V3n0m1010011010/E-Paper-Dev-Board/esp32_epaper_board/kicad/e-paper-esp32/e-paper-esp32.pdf

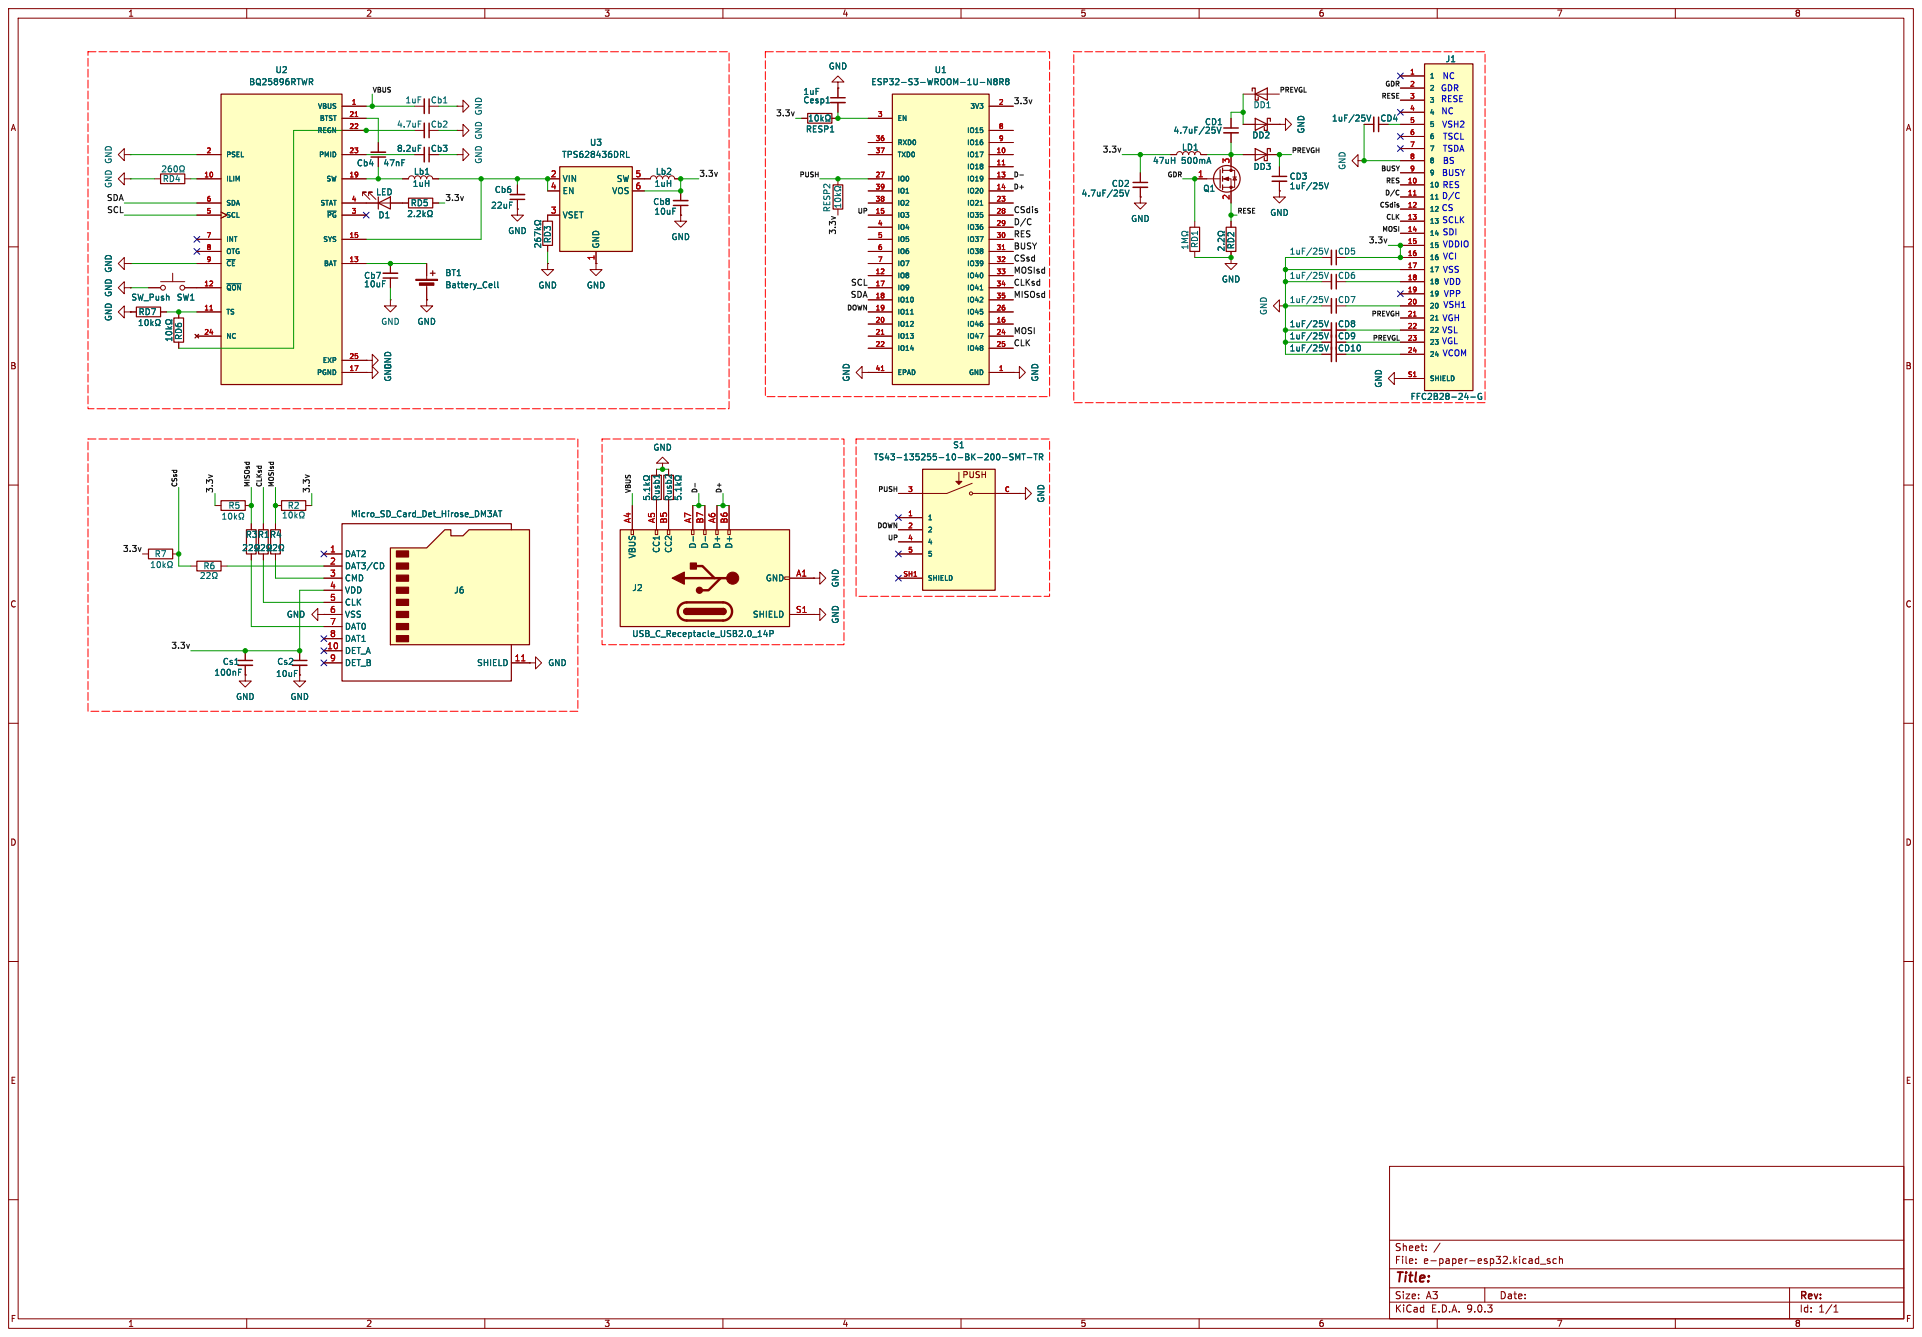
[picture p11: page 1]

1 SW 5 VOS 6 U3 TPS628436DRL RD3 þÿ267k© GND GND GND VBUS

1 SW 5 VOS 6 RD3 þÿ267k© GND

10uFGND GND þÿ5.1k© Rusb1 Rusb2 þÿ5.1k© GND GND

Id: 1/1 Title: File: e-paper-esp32.kicad_sch Sheet: /
