V3n0m1010011010/E-Paper-Dev-Board/esp32_epaper_board/Docs/Plott/e-paper-esp32.pdf

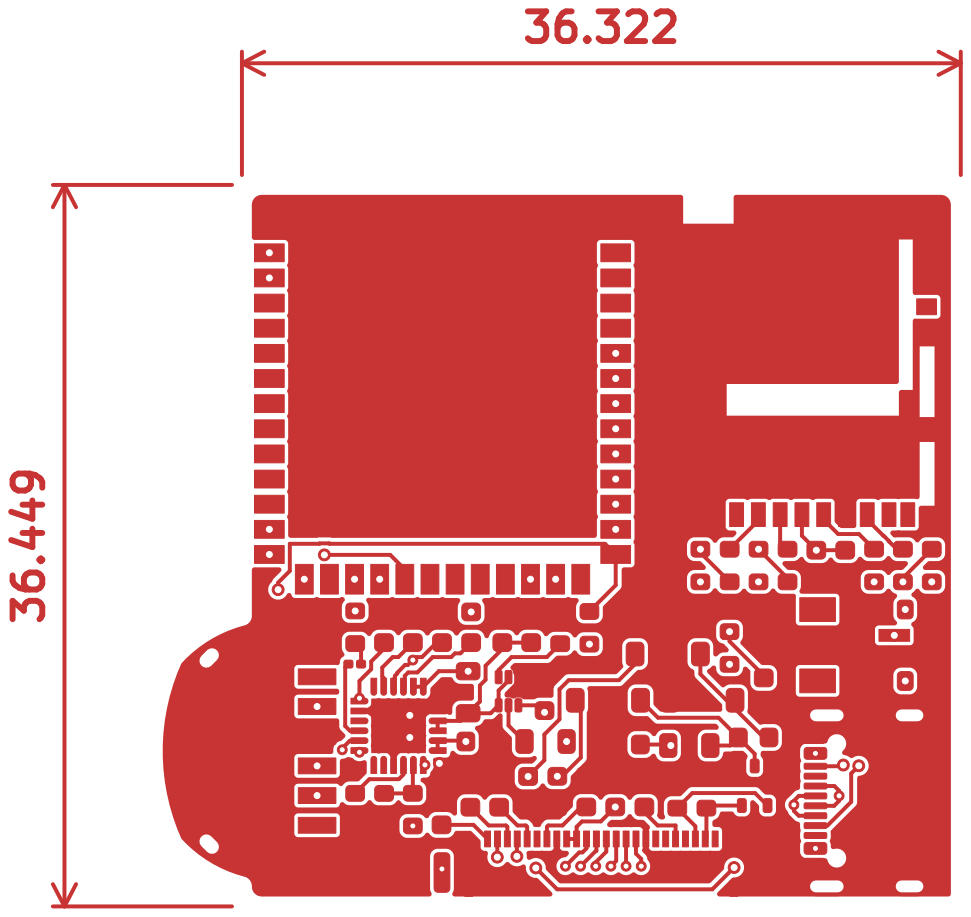
[picture p12: page 1]

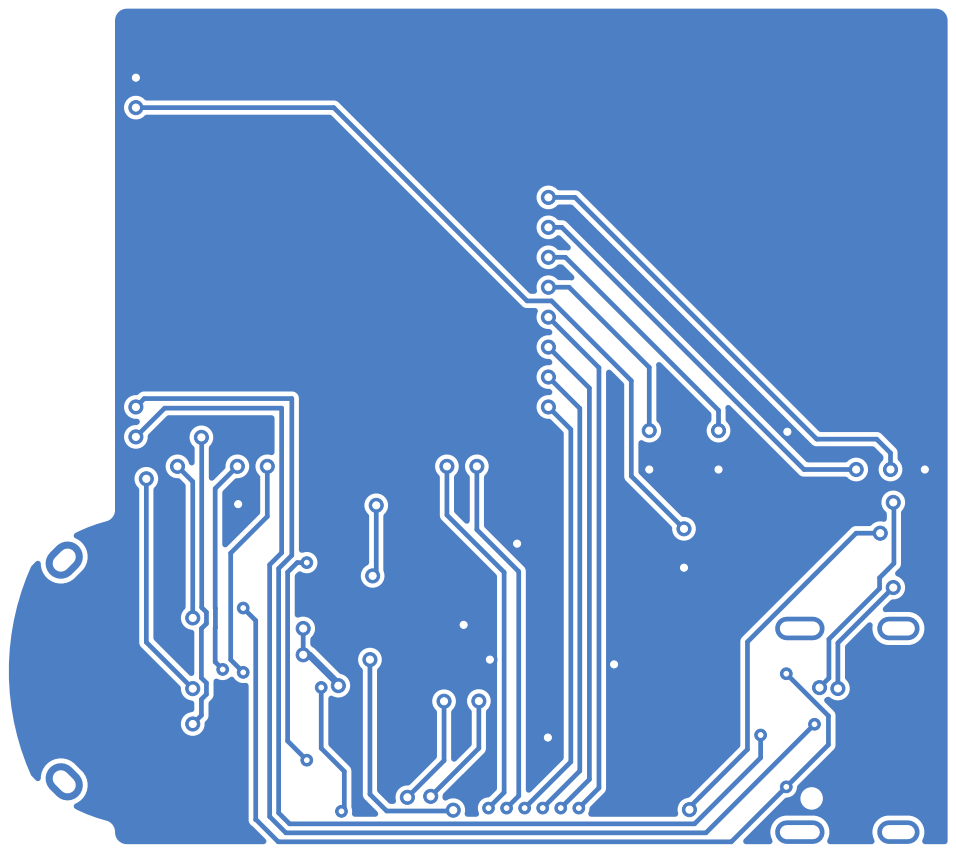
[picture p13: page 2]

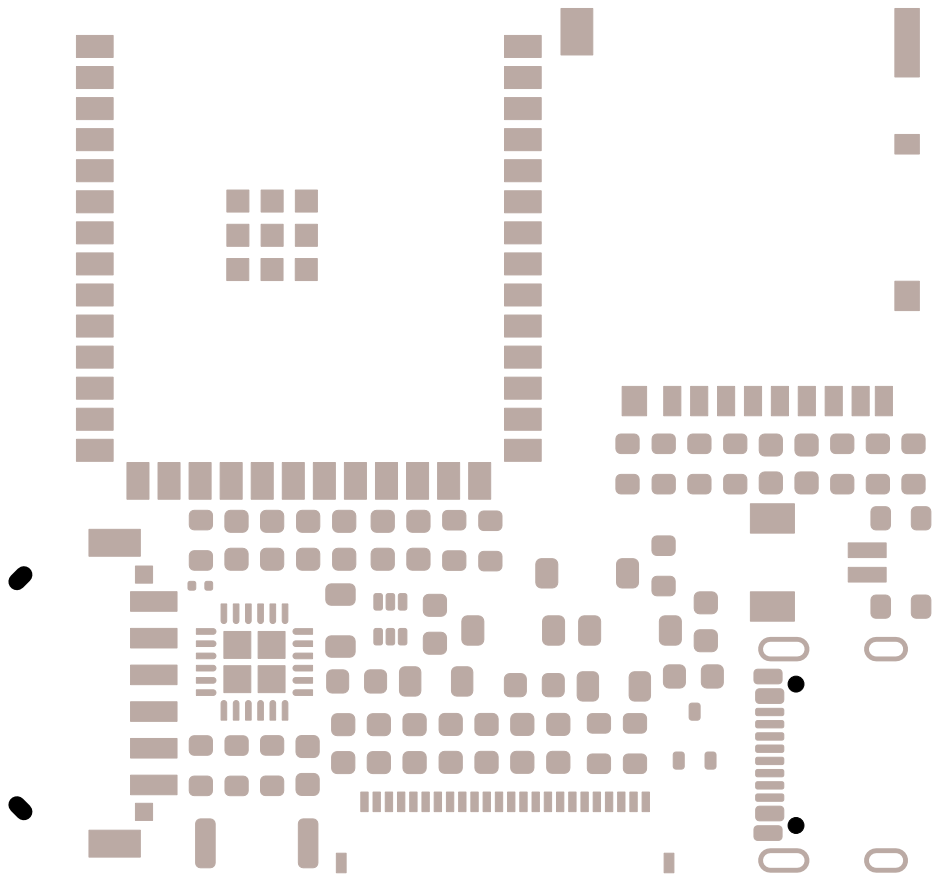
[picture p14: page 3]

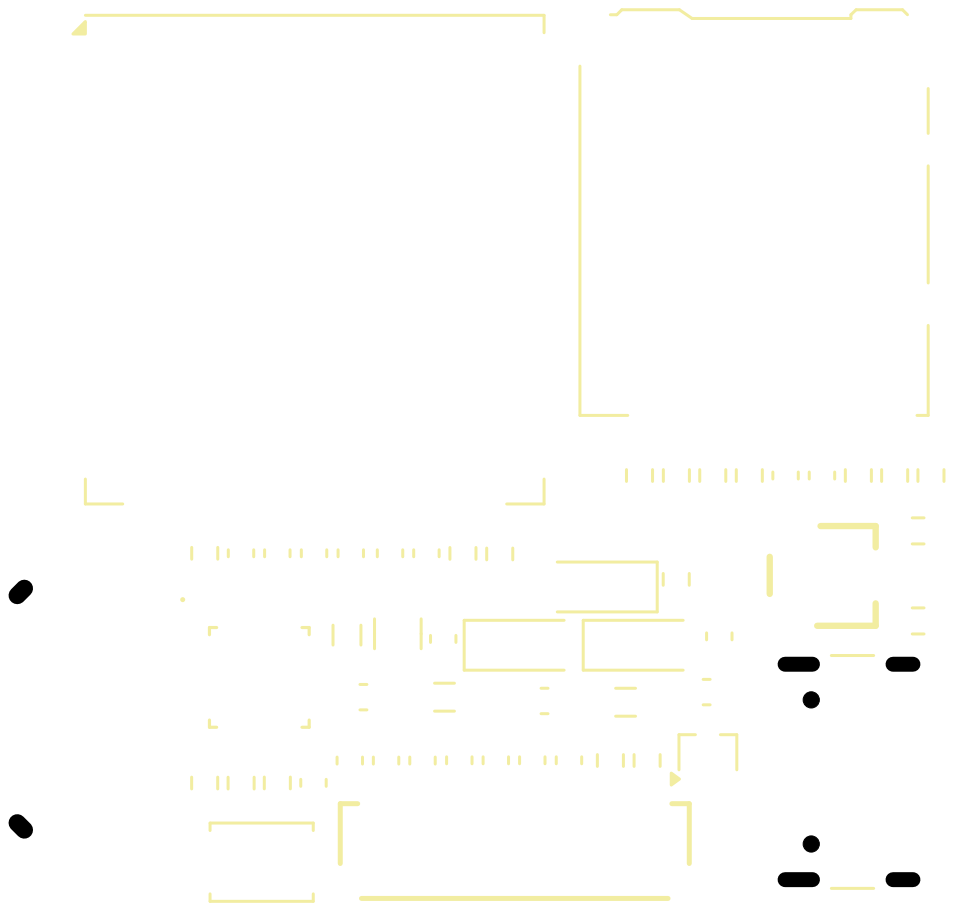
[picture p15: page 5]

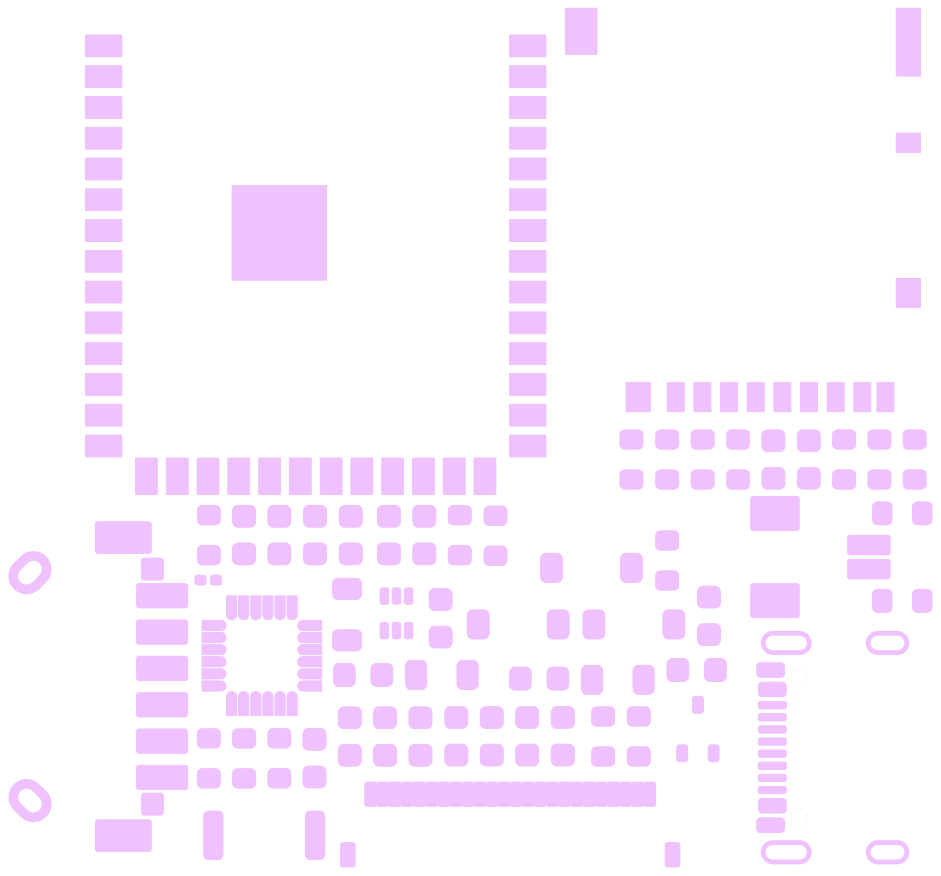
[picture p16: page 7]

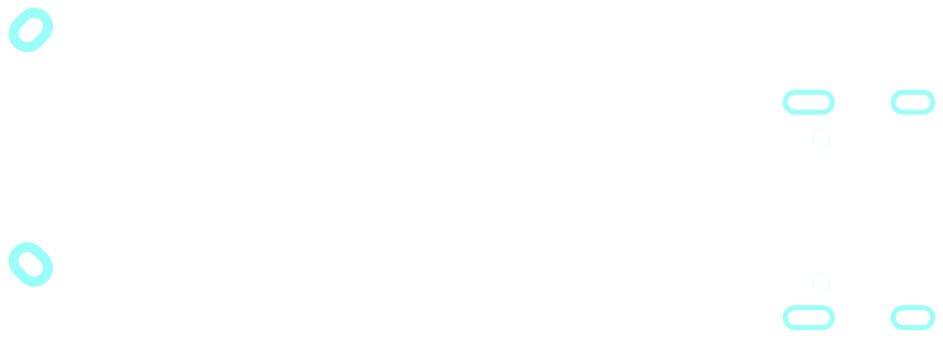
[picture p17: page 8]

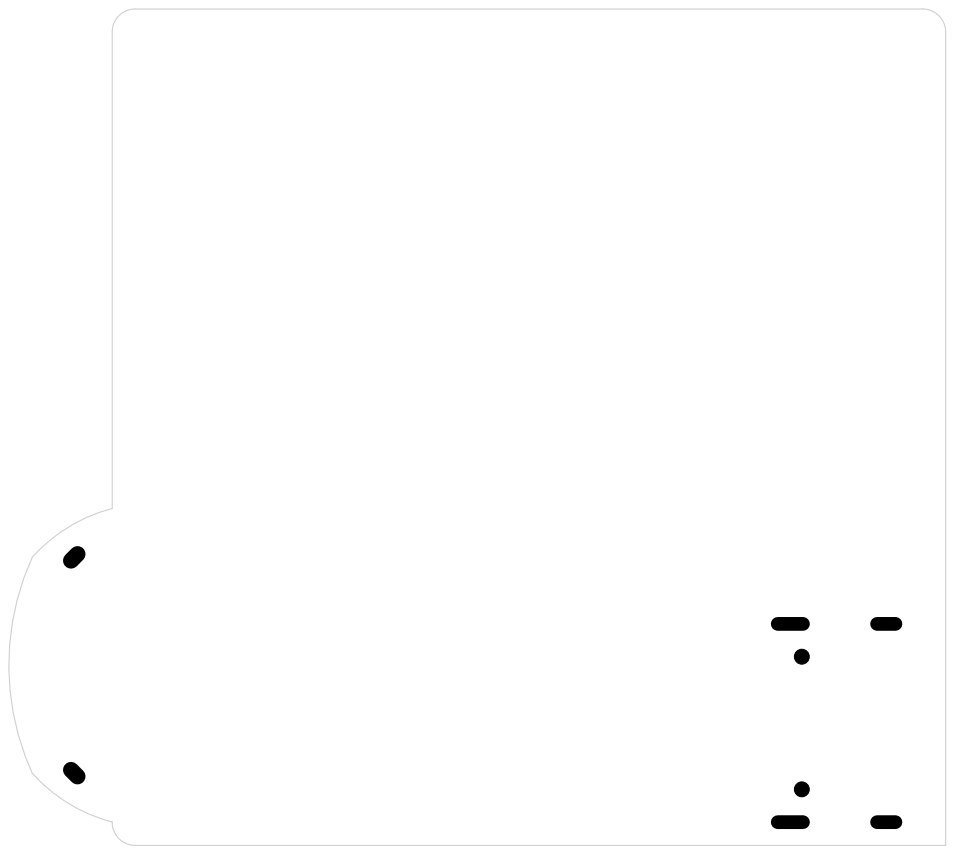
[picture p18: page 9]
